zouppen/virtaboksi/firmware/src/serial.c

#include <stdlib.h>
#include <stdint.h>
#include <stm8.h>
#include "board.h"
#include "serial.h"
#include "timers.h"
#include "settings.h"

#define NUL_TERMINATED 0

// Serial transmit vars
char serial_tx[SERIAL_TX_LEN]; // Outgoing serial data
static const uint8_t *serial_tx_p = serial_tx; // Pointer to tx position
static volatile void *serial_tx_end; // Indicator when to stop sending
static volatile bool tx_state = false; // Is tx start requested
static volatile bool tx_nul_terminated; // Flag for \0 terminated buffer

// Serial receive vars. Using double buffering for rx
static serial_buffer_t rx_buf_a = {0, EMPTY};
static serial_buffer_t rx_buf_b = {0, EMPTY};
static serial_buffer_t *rx_front = NULL; // Current front buffer (NULL if not locked)
static serial_buffer_t *rx_back = &rx_buf_a; // Current back buffer (for populating data)
static char *rx_p = rx_buf_a.data; // Back buffer write pointer
static volatile uint16_t rx_cooldown_left = 0; // To avoid half-duplex clash
static uint16_t modbus_silence;

// (Error) counters
static volatile serial_counter_t counts = {0, 0};

// Prototypes
static void end_of_frame_IM(void);
static void may_send(buflen_t len);
static void transmit_now_IM(void);
static uint16_t get_modbus_silence(void);

// Called from timer interrupt handler when we're between frames.
static void end_of_frame_IM(void)
{
	bool const locked = rx_front != NULL;
	if (locked) {
		// We need to throw a frame overboard
		// because main loop didn't process
		// front buffer in time.
		counts.flip_timeout++;
		goto rewind;
	}

	// Populate length
	rx_back->len = rx_p - rx_back->data;

	// Flip buffers!
	rx_front = rx_back;
	rx_back = (&rx_buf_a == rx_back) ? &rx_buf_b : &rx_buf_a;

rewind:
	// Latest but not least: Rewind receive buffer
	rx_back->state = EMPTY;
	rx_p = rx_back->data;
}

serial_buffer_t *serial_get_message(void) __critical
{
	return rx_front;
}

void serial_free_message(void) __critical
{
	rx_front = NULL;
}

void serial_pull_counters(serial_counter_t *const copy) __critical
{
	*copy = counts;
	counts.flip_timeout = 0;
	counts.too_long_tx = 0;
}

void serial_init(void)
{
	// UART configuration
	UART1_CR2 =
		UART_CR2_TEN |   // Enable TX
		UART_CR2_REN |   // Receiver enable
		UART_CR2_RIEN;   // Receiver interrupt enabled
	// UART1_CR3 default is 1 stop bit
	stm8_uart1_baudrate(settings.baud_rate);

	// Turn on rs485 rx and put to receive mode
	OUTPUT(PIN_TX_EN);
	LOW(PIN_TX_EN);

	// Calculating the 14 bit long duration on the serial line,
	// measured in ticks. We consider a frame to be ready after 14
	// bits and after another 14 bits we can start transmitting.
	// https://en.wikipedia.org/wiki/Modbus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
	uint16_t const ticks_per_sec = 1000000UL / TICK_USEC;
	modbus_silence = (14 * ticks_per_sec - 1) / settings.baud_rate + 1;
}

bool serial_is_transmitting(void)
{
	return tx_state;
}

bool serial_has_message_IM(void)
{
	return rx_front != NULL;
}

void serial_tx_line(void)
{
	// Putting the continuation sign to the end unless it's
	// exactly that long message
	char *const last = serial_tx + SERIAL_TX_LEN - 1;
	if (*last != '\0') {
		*last = '>';
	}

	// Sending until NUL byte, maximum of buffer length
	may_send(NUL_TERMINATED);
}

void serial_tx_bin(buflen_t const len)
{
	// The buffer is allowed to be completely full, that's why
	// comparing greater than instead of greater-than-equals.
	if (len > SERIAL_TX_LEN) {
		// Ignore the whole frame if it's too long.
		__critical {
			counts.too_long_tx++;
		}
		return;
	}

	if (len == 0) {
		// Must not go to transmit phase at all.
		return;
	}

	// Use supplied length
	may_send(len);
}

static void may_send(buflen_t len) __critical
{
	// Setting end pointer accordingly
	if (len == NUL_TERMINATED) {
		// This is a special case, end pointer may be over one
		// char since when it's last char, the line is
		// terminated anyway. This causes one read over buffer
		// but nothing fatal. See UART1_TX interrupt.
		tx_nul_terminated = true;
		serial_tx_end = serial_tx + SERIAL_TX_LEN + 1;
	} else {
		tx_nul_terminated = false;
		serial_tx_end = serial_tx + len;
	}

	// Setting a flag of willingness to perform a transmission
	tx_state = true;

	// RS-485 is half duplex. We need to wait until rx line
	// becomes idle. If it's not, serial_tick calls
	// transmit_now_IM() later.
	if (!rx_cooldown_left) {
		transmit_now_IM();
	}
}

void serial_tick_IM(void) {
	if (!rx_cooldown_left) {
		// Timer has already reached zero
		return;
	}
	if (!--rx_cooldown_left && tx_state) {
		// Timer reached zero and we have something to send.
		transmit_now_IM();
	}
}

static void transmit_now_IM(void)
{
	// Enable RS-485
	HIGH(PIN_TX_EN);

	// Let the TX interrupt to run
	UART1_CR2 |= UART_CR2_TIEN;
}

void serial_int_uart_rx(void) __interrupt(UART1_RXC_ISR)
{
	// Cache values to avoid the register getting cleared. This
	// sequence also clears register values.
	uint8_t const sr = UART1_SR;
	uint8_t const chr = UART1_DR;

	if (sr & UART_SR_FE) {
		// BREAK signal or garbage.
		rx_front->state = BREAK;
		end_of_frame_IM();

		HIGH(PIN_OUT3);
	} else if (sr & UART_SR_RXNE) {
		// Incoming proper data
		LOW(PIN_OUT3);

		// Keep CPU running until we've received a whole message
		timers_stay_awake_IM(SERIAL_KEEPALIVE_TICKS);

		// Resetting rx timers
		rx_cooldown_left = modbus_silence;

		bool const full = rx_p == rx_back->data + SERIAL_RX_LEN;

		if (rx_back->state == OVERFLOW) {
			// Overflow has already happened earlier.
			if (chr == '\n') {
				end_of_frame_IM();
			}
		} else if (chr == '\n') {
			// End of line
			if (!full) {
				// Terminate string
				*rx_p = '\0';
			}
			rx_back->state = TEXT; // FIXME detect text properly
			end_of_frame_IM();
		} else if (full) {
			// Overflow happens now but is not line terminator
			rx_back->state = OVERFLOW;
		} else {
			// We have space for a new char
			*rx_p++ = chr;
		}
	}
}

void serial_int_uart_tx(void) __interrupt(UART1_TXC_ISR)
{
	// Since we share the same interrupt, we have to have check if
	// we have enabled such event before going to check the flags.

	// Check if we are ready to send
	if ((UART1_CR2 & UART_CR2_TIEN) && (UART1_SR & UART_SR_TXE)) {
		uint8_t const out = *serial_tx_p++;

		// Check if we want to transmit more
		bool const buf_end = serial_tx_p == serial_tx_end;
		bool const line_end = tx_nul_terminated && (buf_end || out == '\0');
		if (buf_end || line_end) {
			// This is the last byte. Disable this event
			// and enable rx ready event
			UART1_CR2 ^= UART_CR2_TIEN | UART_CR2_TCIEN;
		}

		// Send byte
		UART1_DR = line_end ? '\n' : out;
	}

	// Check if the transmit is finished
	if ((UART1_CR2 & UART_CR2_TCIEN) && (UART1_SR & UART_SR_TC)) {
		// Transmit finished. Disable this event
		UART1_CR2 &= ~UART_CR2_TCIEN;

		// Turn off RS-485 transmitter
		LOW(PIN_TX_EN);

		// Rewind send buffer
		serial_tx_p = serial_tx;

		// Ready for sleep or for a new send
		tx_state = false;
	}
}
